cmccaskey/BUSINESS-CARD/HARDWARE/MOD/SCHEMATIC.png

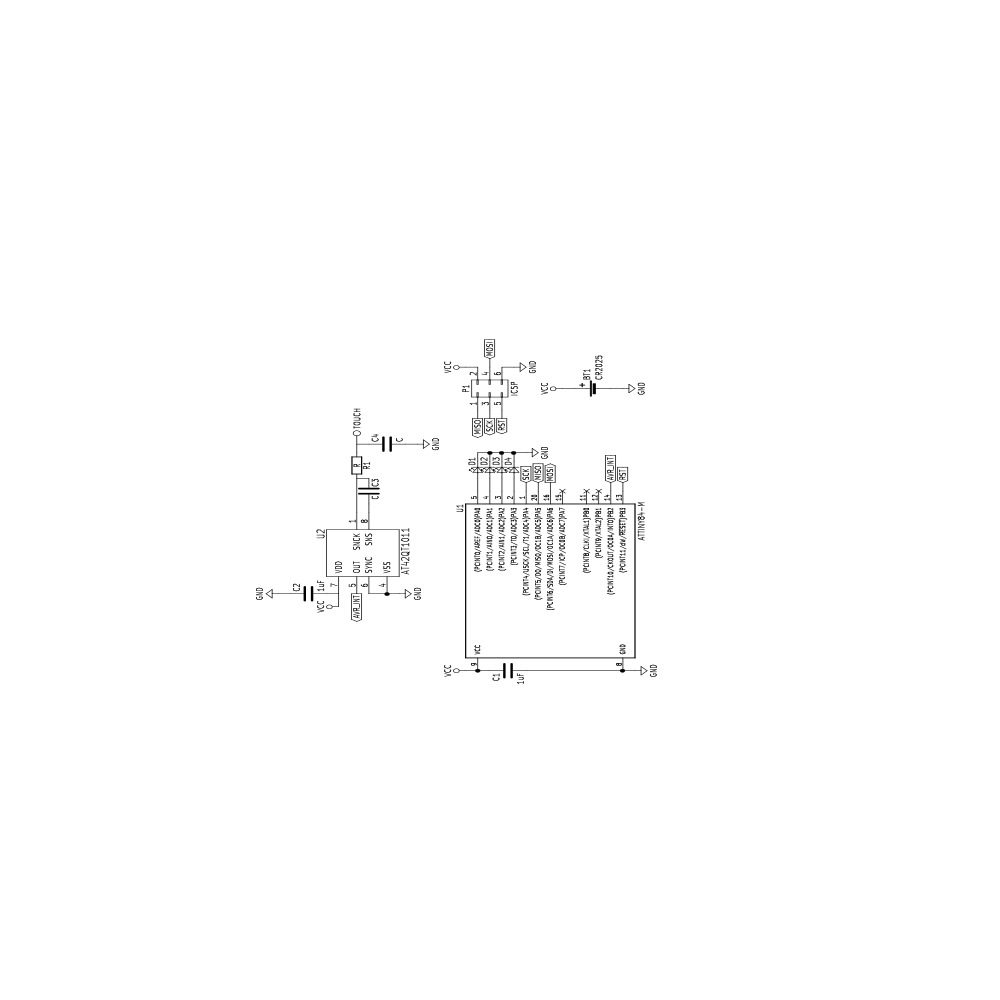
HARDWARE/MOD/SCHEMATIC.png
