cmccaskey/BUSINESS-CARD/IMAGES/BC Front.jpg

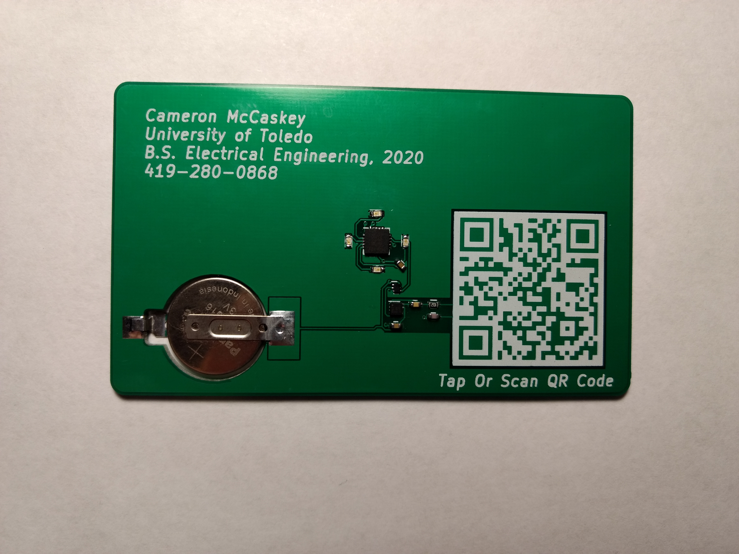
IMAGES/BC Front.jpg
